JatinPatil2003/FollowBot-Balance/Trials_Human_following/Data/pedestrians_5.jpg

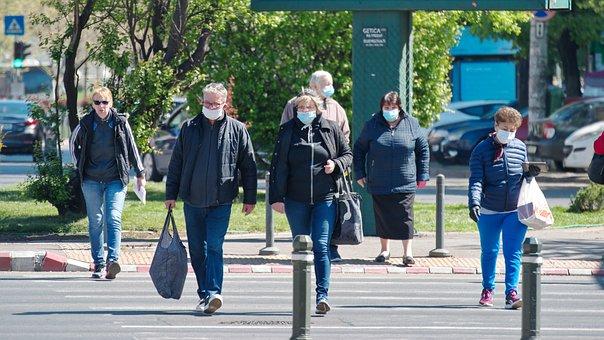
Trials_Human_following/Data/pedestrians_5.jpg
