JatinPatil2003/FollowBot-Balance/Trials_Human_following/Data/pedestrians_3.jpg

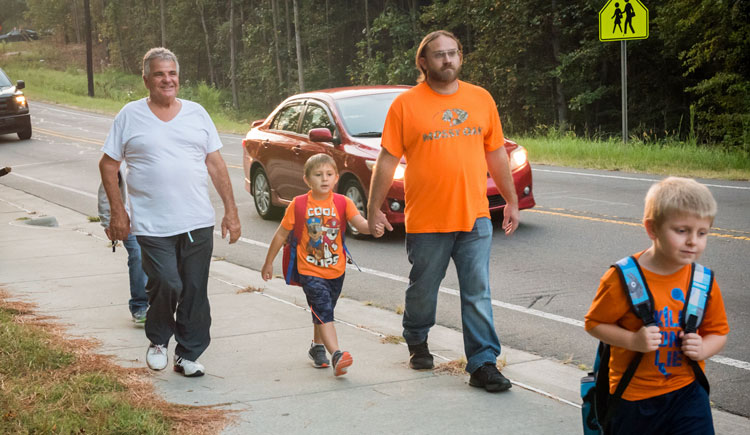
Trials_Human_following/Data/pedestrians_3.jpg
